TickyTacky84/hexaleafs/img/cap.jpg

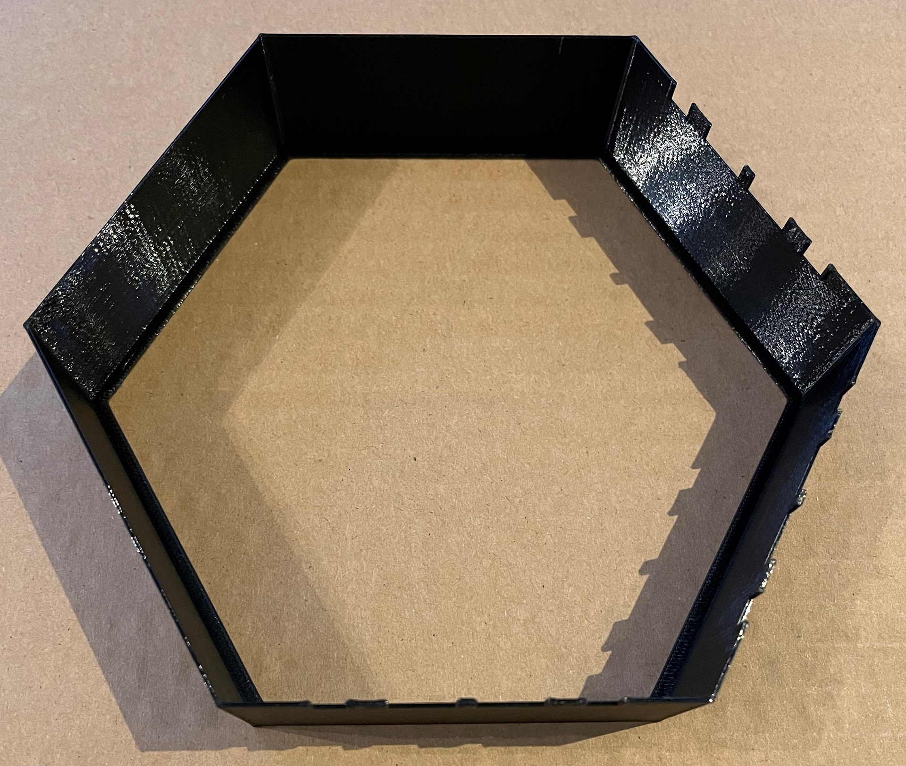
img/cap.jpg
