TickyTacky84/hexaleafs/img/diffusor.jpg

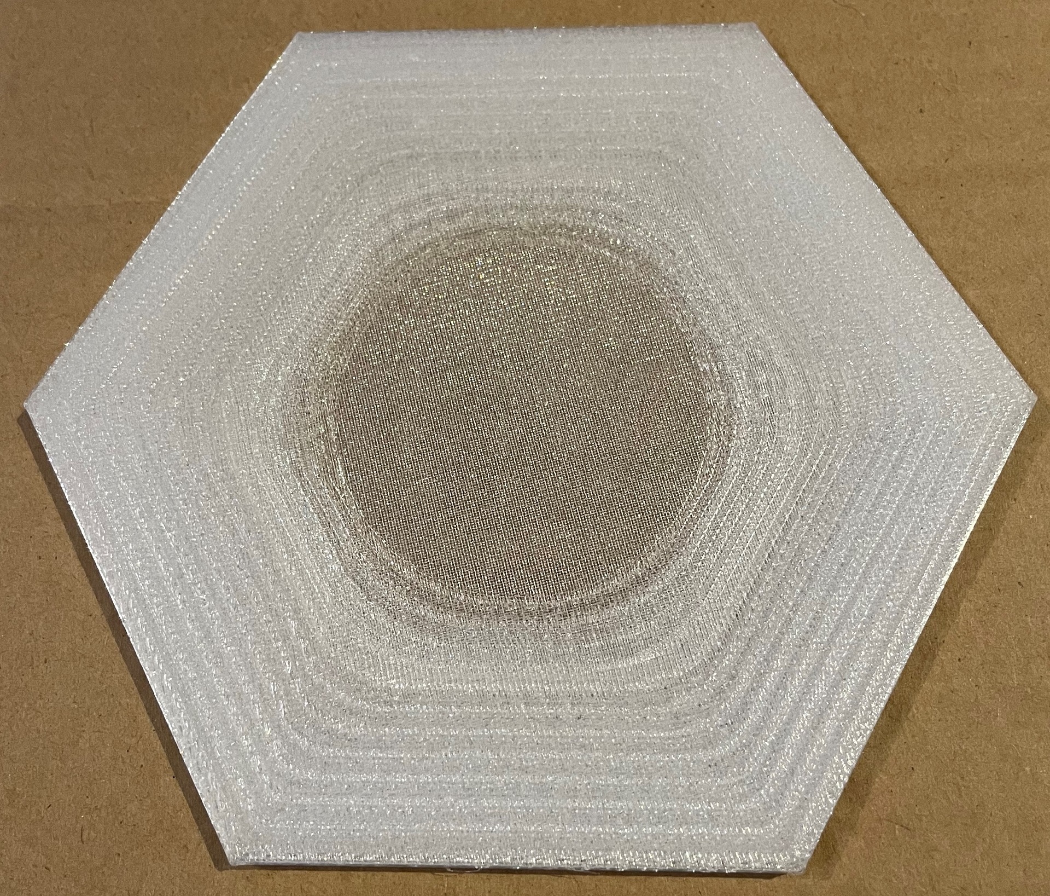
img/diffusor.jpg
