TickyTacky84/hexaleafs/img/rhombus body.jpg

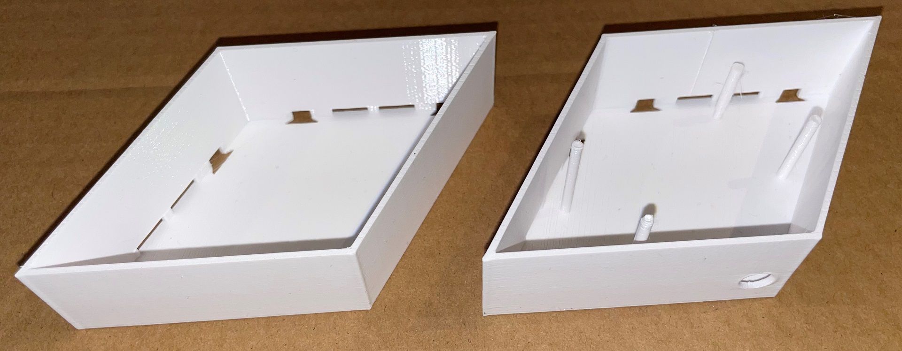
img/rhombus body.jpg
