TickyTacky84/hexaleafs/img/rhombus cap.jpg

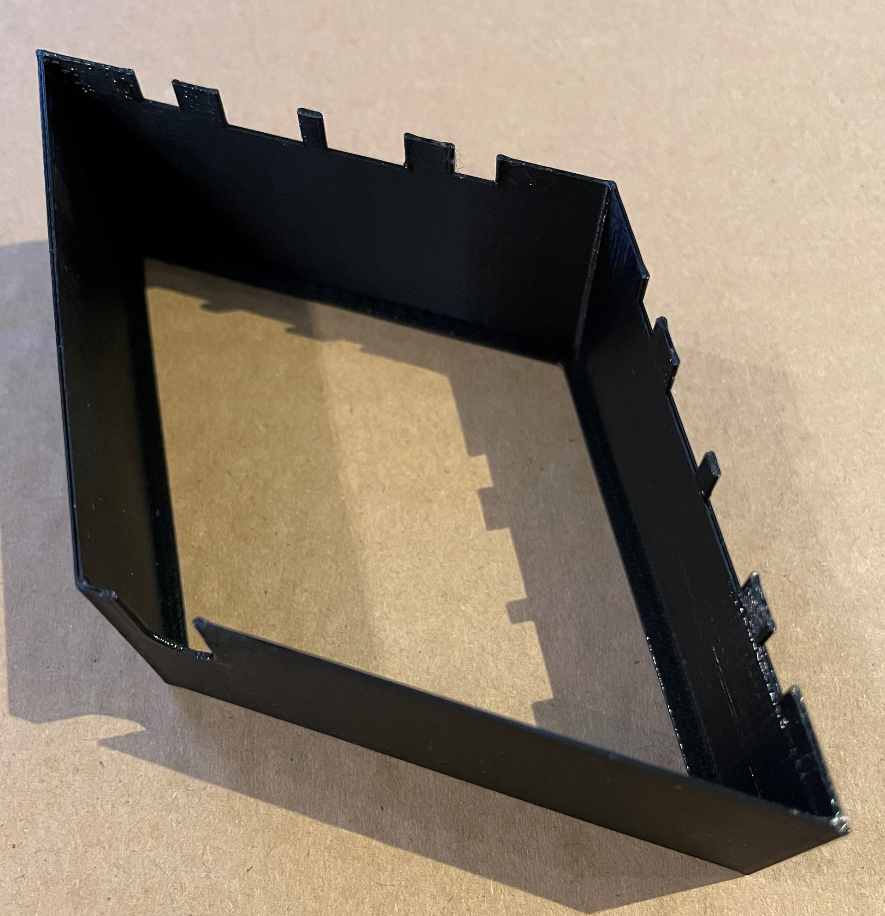
img/rhombus cap.jpg
