TickyTacky84/hexaleafs/img/rhombus face.jpg

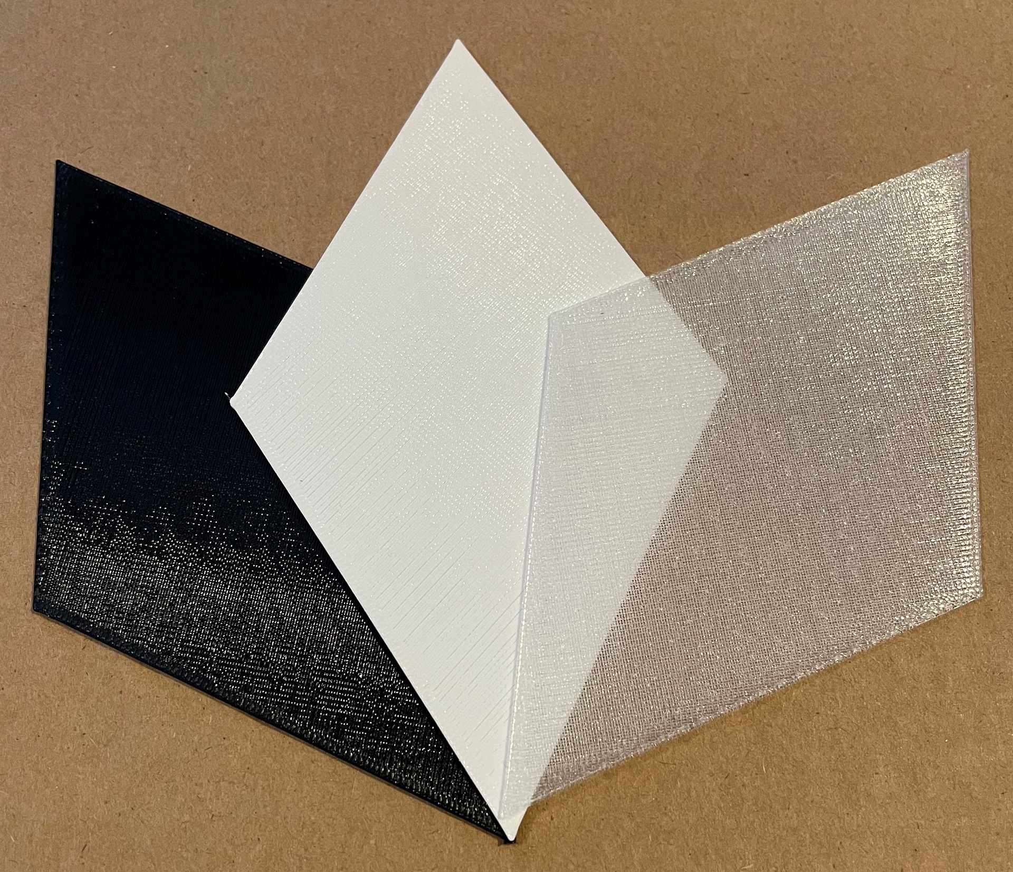
img/rhombus face.jpg
