TickyTacky84/hexaleafs/img/spacer.jpg

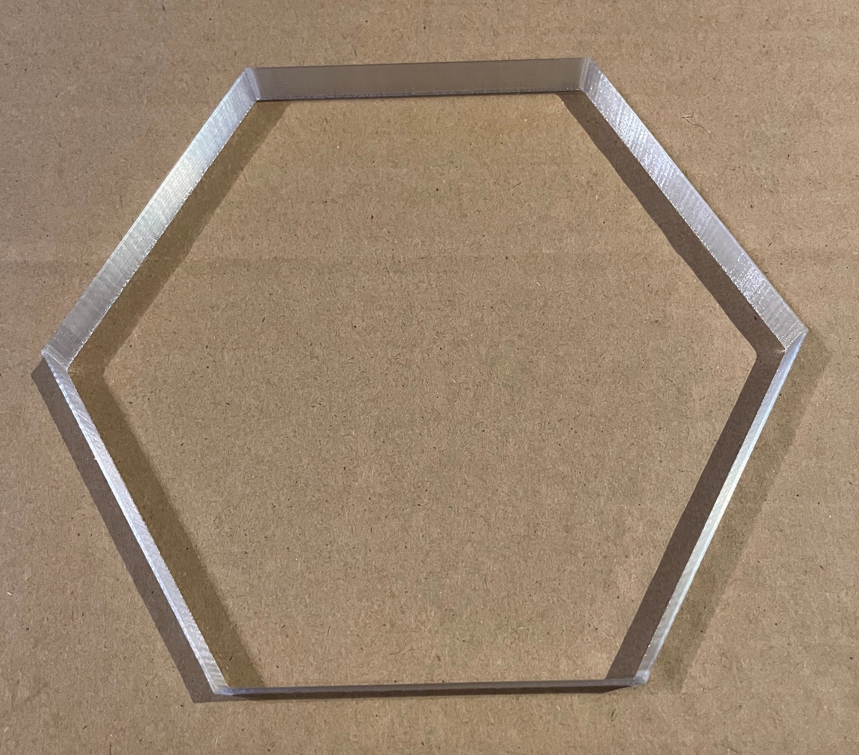
img/spacer.jpg
