TickyTacky84/hexaleafs/stl/clearance_0.3mm/diffusor_5mm.stl

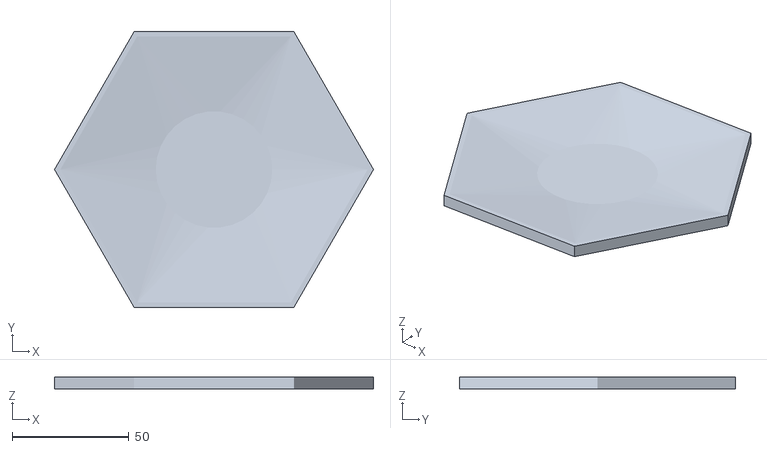
[picture p45: CAD file, 2022-01-23]
stl/clearance_0.3mm/diffusor_5mm.stl
136.9 x 118.6 x 5.00
