TickyTacky84/hexaleafs/stl/clearance_0.3mm/connectorBlind_c_0.2mm.stl

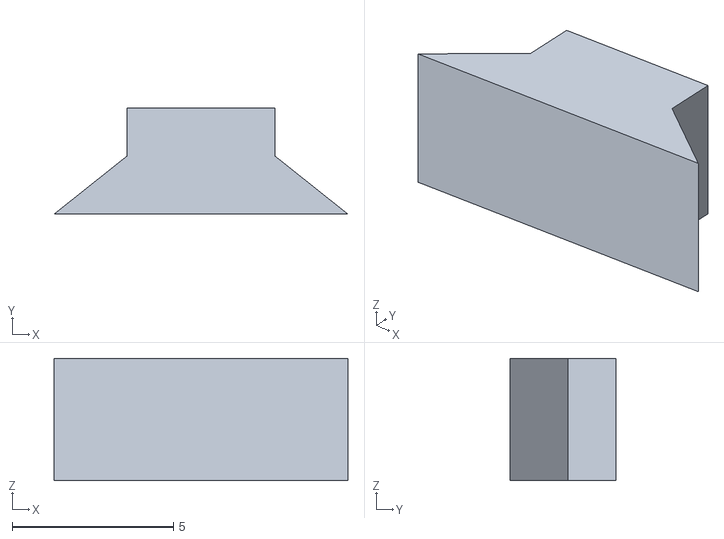
[picture p46: CAD file, 2022-01-23]
stl/clearance_0.3mm/connectorBlind_c_0.2mm.stl
9.12 x 3.30 x 3.80
