TickyTacky84/hexaleafs/stl/clearance_0.3mm/connector_c_0.1mm_default.stl

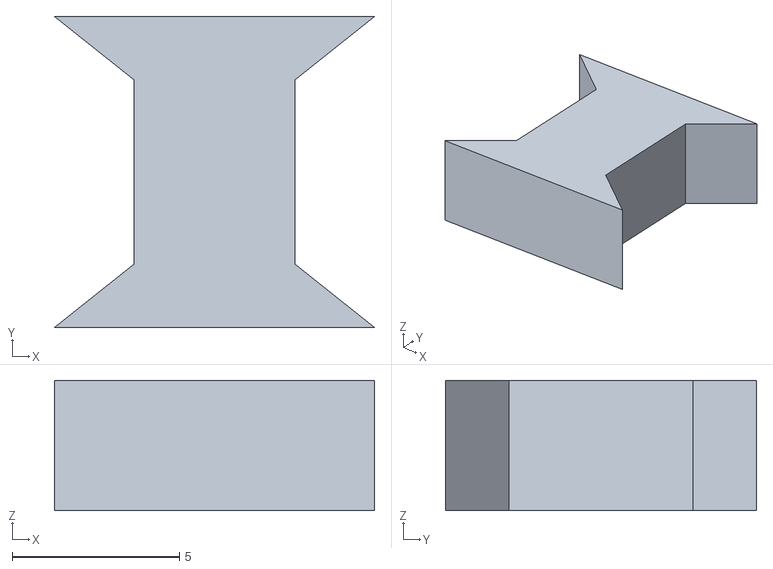
[picture p47: CAD file, 2022-01-23]
stl/clearance_0.3mm/connector_c_0.1mm_default.stl
9.57 x 9.30 x 3.90
