TickyTacky84/hexaleafs/stl/clearance_0.3mm/connector_c_0.2mm.stl

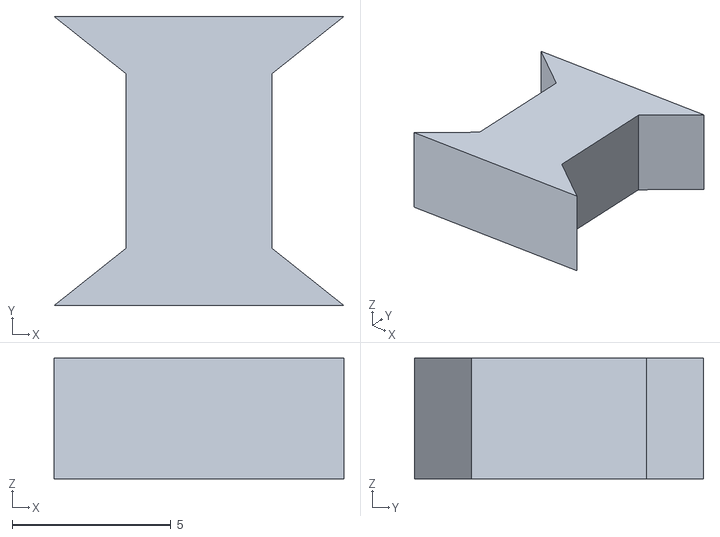
[picture p48: CAD file, 2022-01-23]
stl/clearance_0.3mm/connector_c_0.2mm.stl
9.12 x 9.10 x 3.80
