TickyTacky84/hexaleafs/stl/clearance_0.3mm/connectorBlind_c_0.3mm.stl

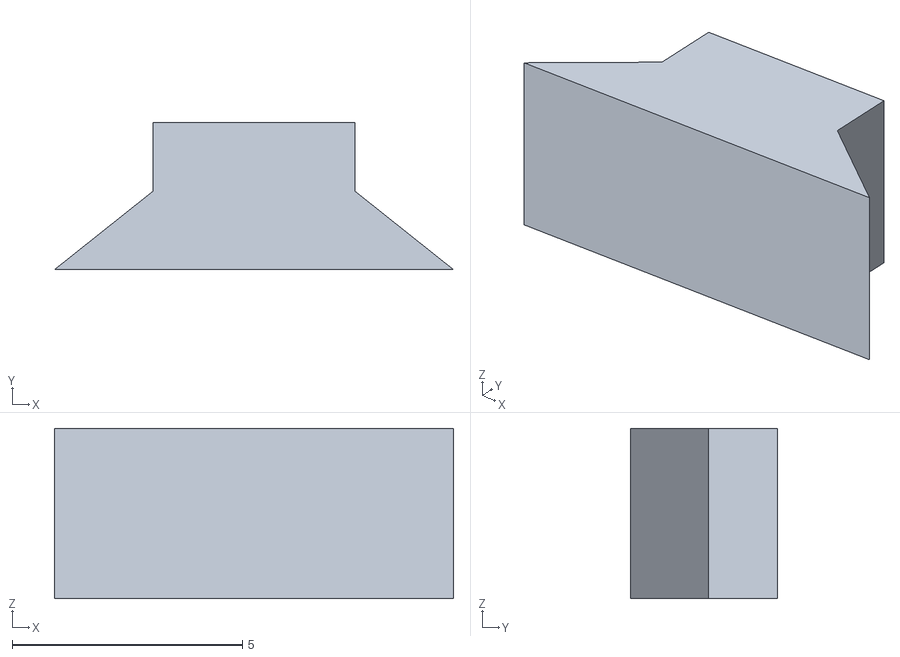
[picture p49: CAD file, 2022-01-23]
stl/clearance_0.3mm/connectorBlind_c_0.3mm.stl
8.67 x 3.20 x 3.70
