TickyTacky84/hexaleafs/stl/clearance_0.3mm/connector_c_0.4mm.stl

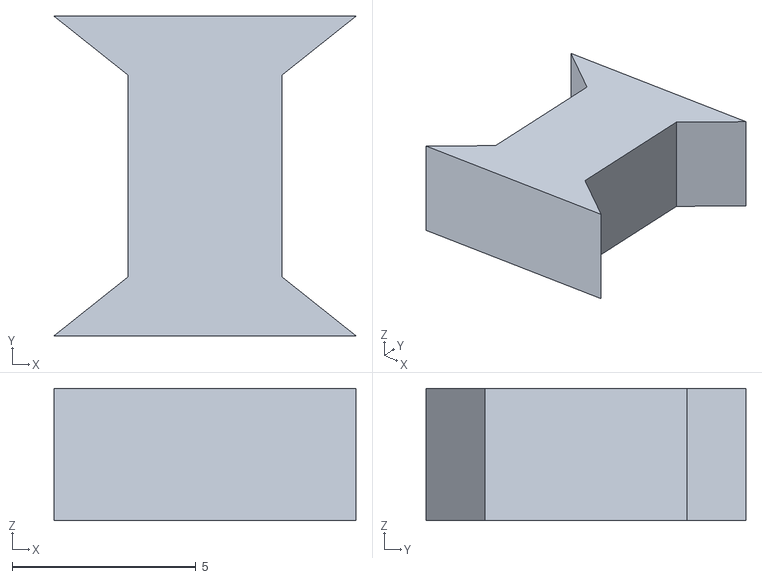
[picture p50: CAD file, 2022-01-23]
stl/clearance_0.3mm/connector_c_0.4mm.stl
8.22 x 8.70 x 3.60
